distinctm1nd/2025_utahtastic_bsides_badge/hardware/2025_bsides_badge_v2.kicad_sch

## KiCad design hardware/2025_bsides_badge_v2.kicad_sch (2024-11-23)

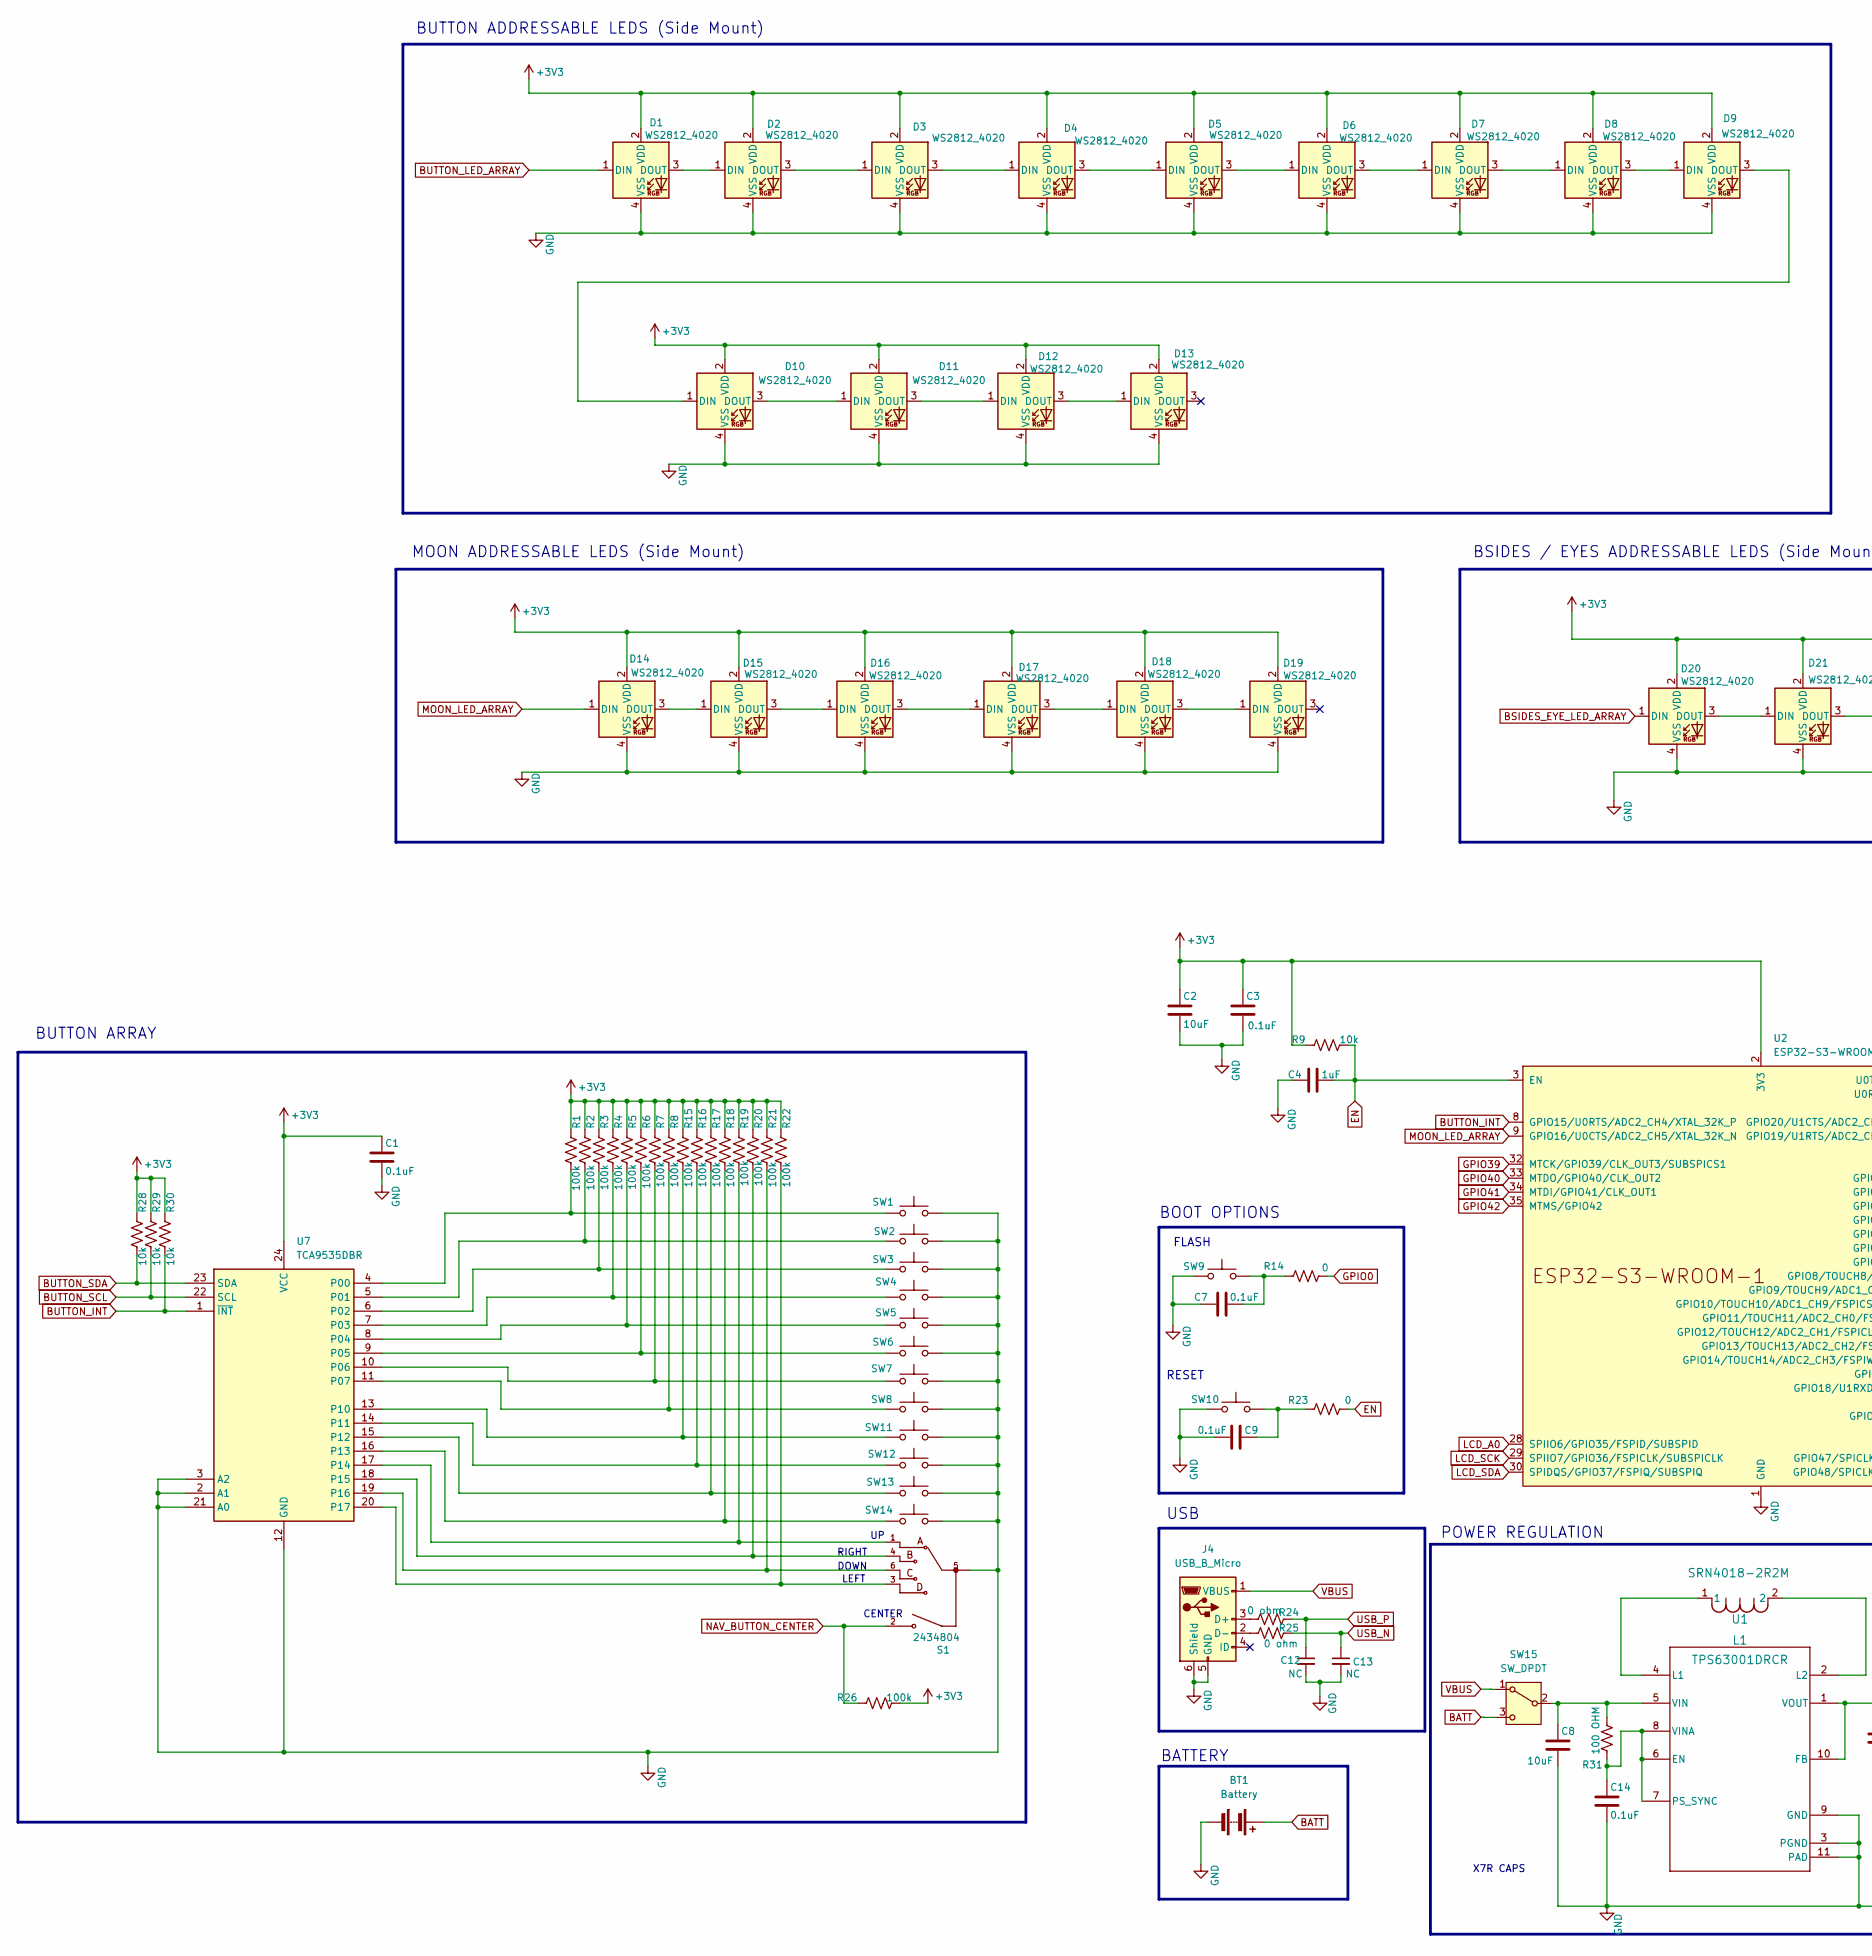
[picture p5: schematic 2025_bsides_badge_v2.kicad_sch, part in row 1, column 1]

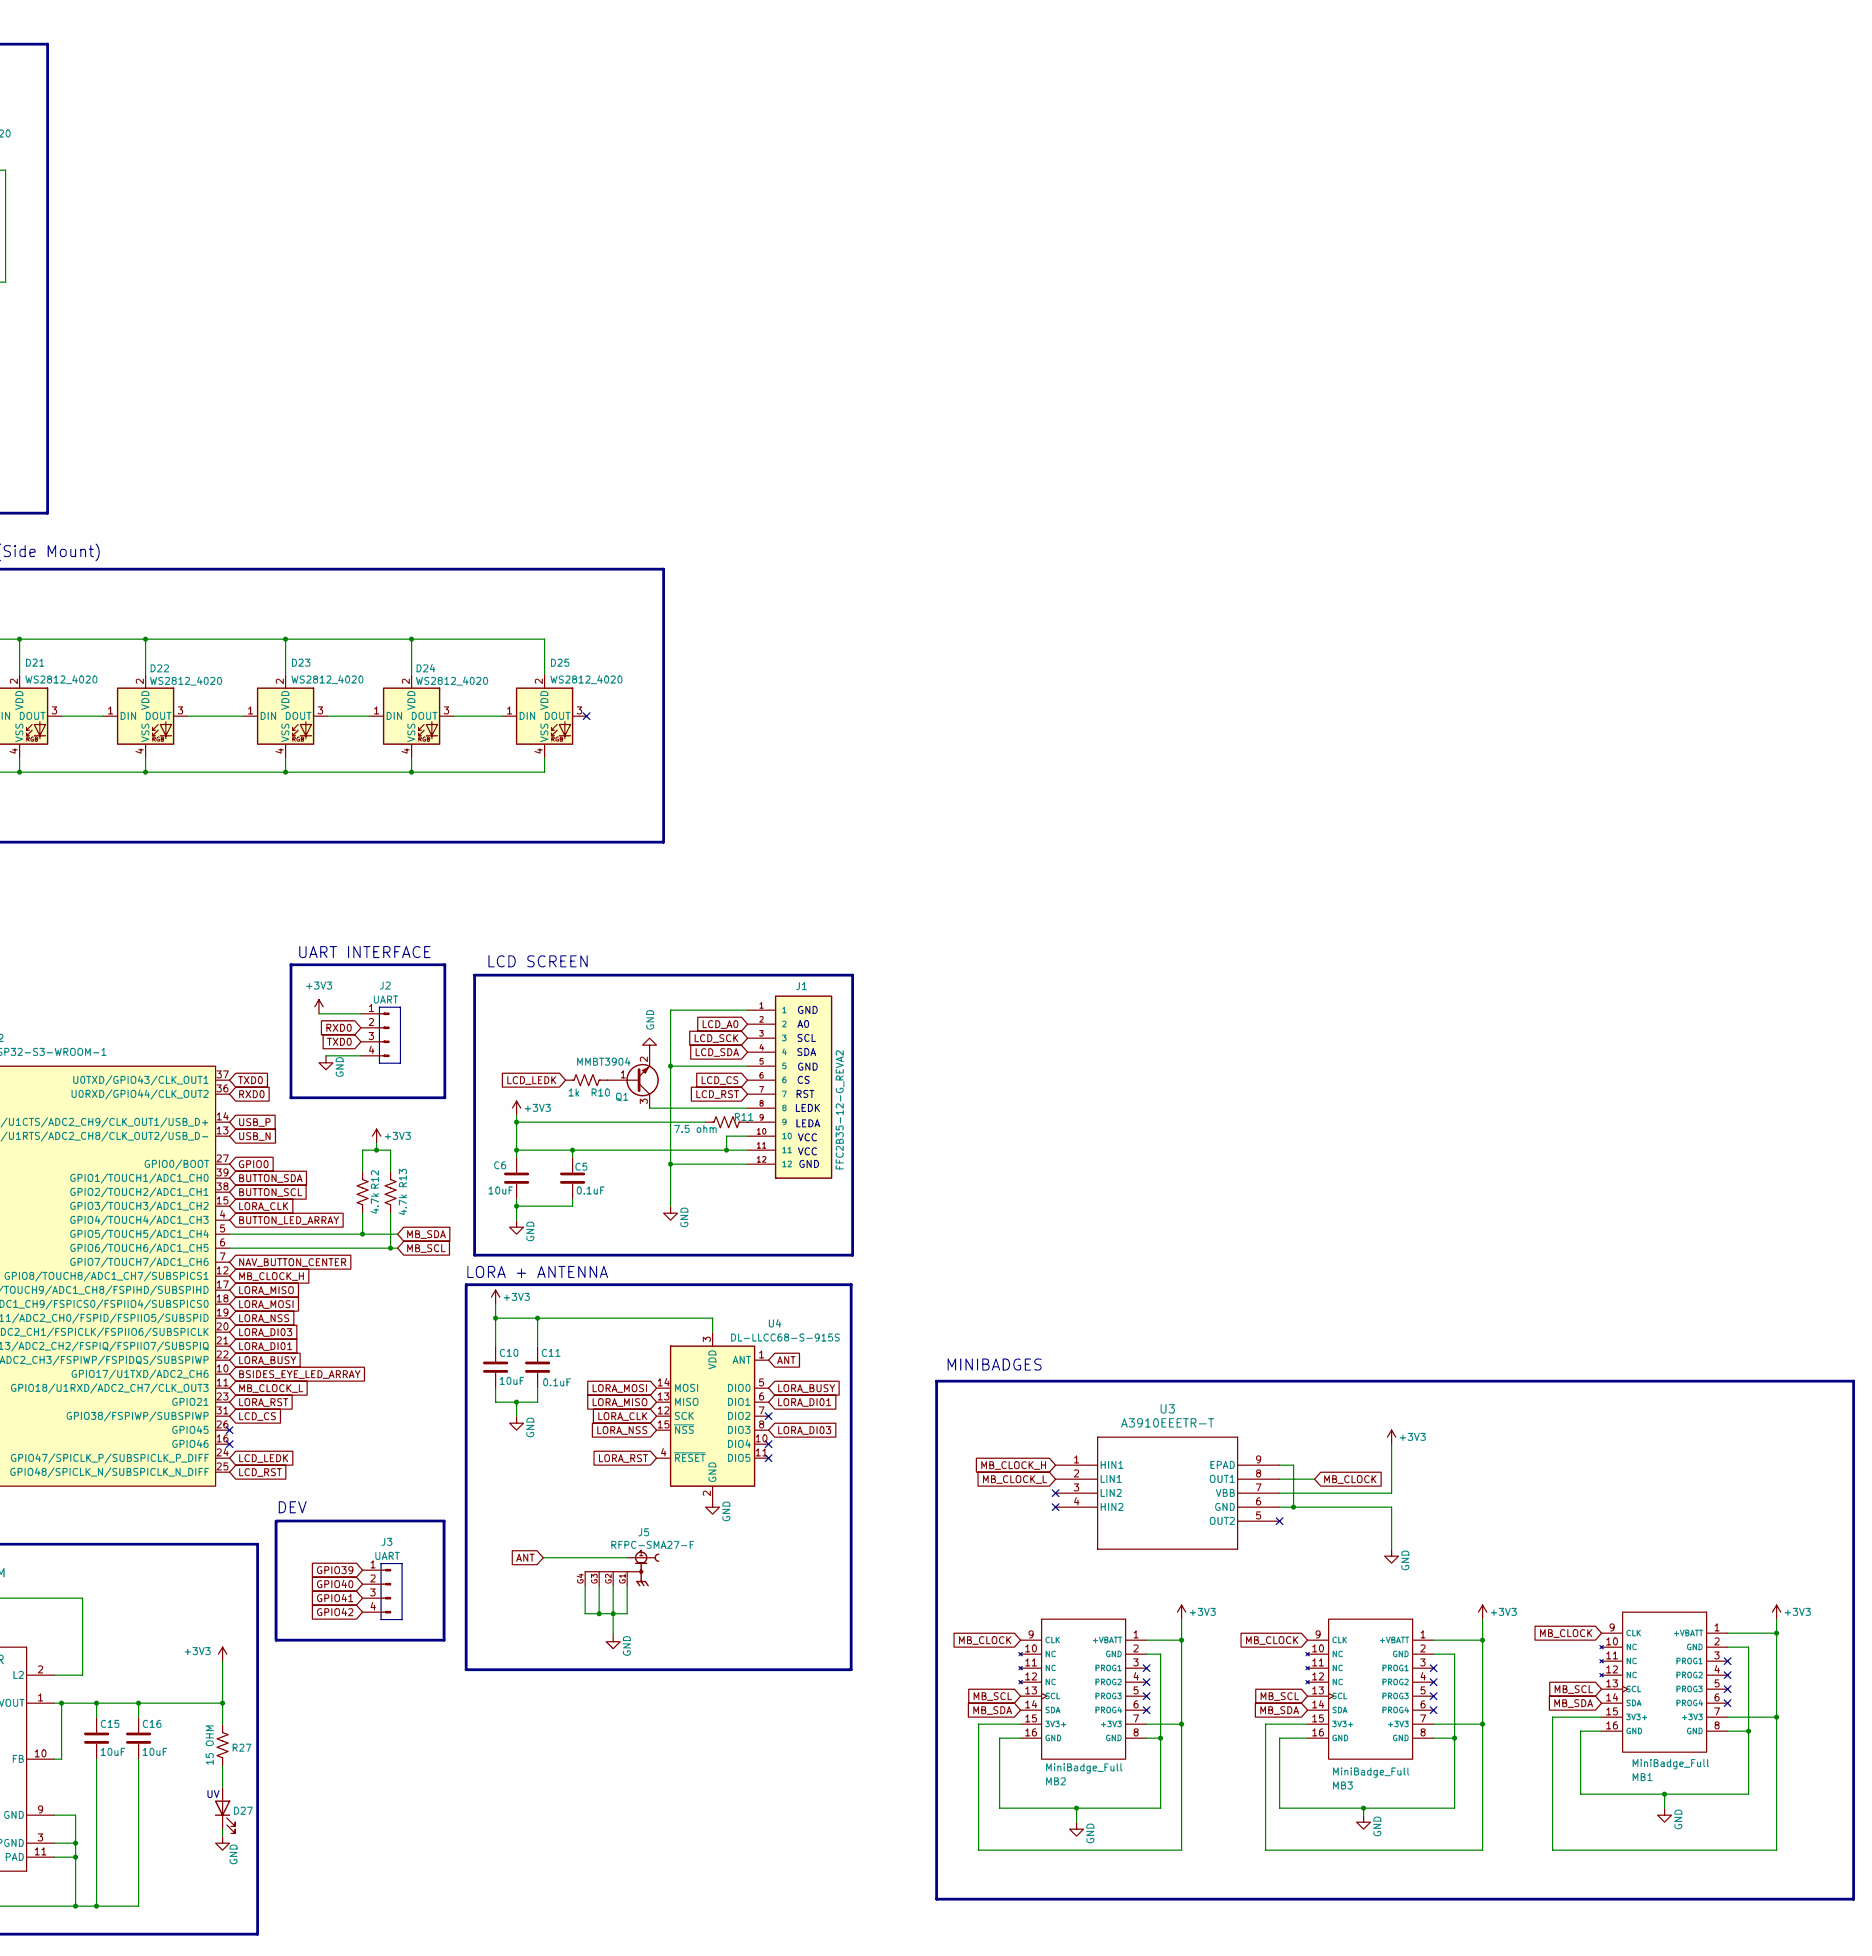
[picture p6: schematic 2025_bsides_badge_v2.kicad_sch, part in row 1, column 2]

Parts:
BT1: Battery; mad_hatter_3_AA_battery
C1, C3, C5, C7, C9, C11, C14: 0.1uF; C_0603_1608Metric_Pad1.08x0.95mm_HandSolder
C2, C6, C8, C10, C15, C16: 10uF; C_0805_2012Metric_Pad1.18x1.45mm_HandSolder
C4: 1uF; C_0603_1608Metric_Pad1.08x0.95mm_HandSolder
C12, C13: NC; C_0603_1608Metric_Pad1.08x0.95mm_HandSolder
D1, D2, D3, D4, D5, D6, D7, D8, D9, D10, D11, D12, D13, D14, D15, D16, D17, D18, D19, D20, D21, D22, D23, D24, D25: WS2812_4020; sk6812-side-a
D27: LED; LED_1206_3216Metric_Pad1.42x1.75mm_HandSolder
J1: FFC2B35-12-G_REVA2; GCT_FFC2B35-12-G_REVA2; PARTREV A2
J2, J3: UART; mad_hatter_sneaky_uart_connector
J4: USB_B_Micro; USB_Micro-B_Amphenol_10118193-0001LF_Horizontal
J5: RFPC-SMA27-F; bsides_RFPC_SMA27_F; PARTREV 1.0
L1: SRN4018-2R2M; L_Bourns-SRN4018
MB1, MB2, MB3: MiniBadge_Full; MiniBadge_Slot_Basic
Q1: MMBT3904; SOT-23
R1, R2, R3, R4, R5, R6, R7, R8, R15, R16, R17, R18, R19, R20, R21, R22, R26: 100k; R_0603_1608Metric_Pad0.98x0.95mm_HandSolder
R9, R28, R29, R30: 10k; R_0603_1608Metric_Pad0.98x0.95mm_HandSolder
R10: 1k; R_0603_1608Metric_Pad0.98x0.95mm_HandSolder
R11: 7.5 ohm; R_0603_1608Metric_Pad0.98x0.95mm_HandSolder
R12, R13: 4.7k; R_0603_1608Metric_Pad0.98x0.95mm_HandSolder
R14, R23: 0; R_0603_1608Metric_Pad0.98x0.95mm_HandSolder
R24, R25: 0 ohm; R_0603_1608Metric_Pad0.98x0.95mm_HandSolder
R27: 15 OHM; R_0603_1608Metric_Pad0.98x0.95mm_HandSolder
R31: 100 OHM; R_0603_1608Metric_Pad0.98x0.95mm_HandSolder
S1: 2434804; nav_switch_2434804_1; PARTREV A
SW1, SW2, SW3, SW4, SW5, SW6, SW7, SW8, SW9, SW10, SW11, SW12, SW13, SW14: SW_Push; button_switch_TL3305A
SW15: SW_DPDT; js202011jaqn
U1: TPS63001DRCR; Texas_DRC0010J
U2: ESP32-S3-WROOM-1
U3: A3910EEETR-T; DFN-8_ALM
U4: DL-LLCC68-S-915S; Ai-Thinker-Ra-01-LoRa
U7: TCA9535DBR; SSOP-24_5.3x8.2mm_P0.65mm

Connections:
+3V3: C1.1, C2.1, C3.1, C5.1, C6.1, C10.1, C11.1, C15.1, C16.1, D1.2 (VDD), D2.2 (VDD), D3.2 (VDD), D4.2 (VDD), D5.2 (VDD), D6.2 (VDD), D7.2 (VDD), D8.2 (VDD), D9.2 (VDD), D10.2 (VDD), D11.2 (VDD), D12.2 (VDD), D13.2 (VDD), D14.2 (VDD), D15.2 (VDD), D16.2 (VDD), D17.2 (VDD), D18.2 (VDD), D19.2 (VDD), D20.2 (VDD), D21.2 (VDD), D22.2 (VDD), D23.2 (VDD), D24.2 (VDD), D25.2 (VDD), J1.10, J1.11, J2.1, MB1.1 (+VBATT), MB1.7 (+3V3), MB1.15 (3V3+), MB2.1 (+VBATT), MB2.7 (+3V3), MB2.15 (3V3+), MB3.1 (+VBATT), MB3.7 (+3V3), MB3.15 (3V3+), R1.1, R2.1, R3.1, R4.1, R5.1, R6.1, R7.1, R8.1, R9.1, R11.1, R12.2, R13.2, R15.1, R16.1, R17.1, R18.1, R19.1, R20.1, R21.1, R22.1, R26.2, R27.1, R28.1, R29.1, R30.1, U1.1 (VOUT), U1.10 (FB), U2.2 (3V3), U3.7 (VBB), U4.3 (VDD), U7.24 (VCC)
ANT: J5.1, U4.1 (ANT)
BATT: BT1.1 (+), SW15.3 (C)
BSIDES_EYE_LED_ARRAY: D20.1 (DIN), U2.10 (GPIO17/U1TXD/ADC2_CH6)
BUTTON_INT: R30.2, U2.8 (GPIO15/U0RTS/ADC2_CH4/XTAL_32K_P), U7.1 (~INT)
BUTTON_LED_ARRAY: D1.1 (DIN), U2.4 (GPIO4/TOUCH4/ADC1_CH3)
BUTTON_SCL: R29.2, U2.38 (GPIO2/TOUCH2/ADC1_CH1), U7.22 (SCL)
BUTTON_SDA: R28.2, U2.39 (GPIO1/TOUCH1/ADC1_CH0), U7.23 (SDA)
EN: C4.1, R9.2, R23.2, U2.3 (EN)
GND: BT1.2 (-), C1.2, C2.2, C3.2, C4.2, C5.2, C6.2, C7.2, C8.2, C9.2, C10.2, C11.2, C12.2, C13.2, C14.2, C15.2, C16.2, D1.4 (VSS), D2.4 (VSS), D3.4 (VSS), D4.4 (VSS), D5.4 (VSS), D6.4 (VSS), D7.4 (VSS), D8.4 (VSS), D9.4 (VSS), D10.4 (VSS), D11.4 (VSS), D12.4 (VSS), D13.4 (VSS), D14.4 (VSS), D15.4 (VSS), D16.4 (VSS), D17.4 (VSS), D18.4 (VSS), D19.4 (VSS), D20.4 (VSS), D21.4 (VSS), D22.4 (VSS), D23.4 (VSS), D24.4 (VSS), D25.4 (VSS), D27.1 (K), J1.1, J1.5, J1.12, J2.4, J4.5 (GND), J4.6 (Shield), J5.G1, J5.G2, J5.G3, J5.G4, MB1.2 (GND), MB1.8 (GND), MB1.16 (GND), MB2.2 (GND), MB2.8 (GND), MB2.16 (GND), MB3.2 (GND), MB3.8 (GND), MB3.16 (GND), Q1.2 (E), S1.5, SW1.2, SW2.2, SW3.2, SW4.2, SW5.2, SW6.2, SW7.2, SW8.2, SW9.1, SW10.1, SW11.2, SW12.2, SW13.2, SW14.2, U1.3 (PGND), U1.9 (GND), U1.11 (PAD), U2.1 (GND), U2.40 (GND), U2.41 (GND), U3.6 (GND), U3.9 (EPAD), U4.2 (GND), U4.9 (GND), U4.16 (GND), U7.2 (A1), U7.3 (A2), U7.12 (GND), U7.21 (A0)
GPIO0: R14.2, U2.27 (GPIO0/BOOT)
GPIO39: J3.1, U2.32 (MTCK/GPIO39/CLK_OUT3/SUBSPICS1)
GPIO40: J3.2, U2.33 (MTDO/GPIO40/CLK_OUT2)
GPIO41: J3.3, U2.34 (MTDI/GPIO41/CLK_OUT1)
GPIO42: J3.4, U2.35 (MTMS/GPIO42)
LCD_A0: J1.2, U2.28 (SPIIO6/GPIO35/FSPID/SUBSPID)
LCD_CS: J1.6, U2.31 (GPIO38/FSPIWP/SUBSPIWP)
LCD_LEDK: R10.1, U2.24 (GPIO47/SPICLK_P/SUBSPICLK_P_DIFF)
LCD_RST: J1.7, U2.25 (GPIO48/SPICLK_N/SUBSPICLK_N_DIFF)
LCD_SCK: J1.3, U2.29 (SPIIO7/GPIO36/FSPICLK/SUBSPICLK)
LCD_SDA: J1.4, U2.30 (SPIDQS/GPIO37/FSPIQ/SUBSPIQ)
LORA_BUSY: U2.22 (GPIO14/TOUCH14/ADC2_CH3/FSPIWP/FSPIDQS/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), U4.5 (DIO0)
LORA_CLK: U2.15 (GPIO3/TOUCH3/ADC1_CH2), U4.12 (SCK)
LORA_DI01: U2.21 (GPIO13/TOUCH13/ADC2_CH2/FSPIQ/FSPIIO7/S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), U4.6 (DIO1)
LORA_DI03: U2.20 (GPIO12/TOUCH12/ADC2_CH1/FSPICLK/FSPIIO6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), U4.8 (DIO3)
LORA_MISO: U2.17 (GPIO9/TOUCH9/ADC1_CH8/FSPIHD/SUBSPIHD), U4.13 (MISO)
LORA_MOSI: U2.18 (GPIO10/TOUCH10/ADC1_CH9/FSPICS0/FSPIIO4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), U4.14 (MOSI)
LORA_NSS: U2.19 (GPIO11/TOUCH11/ADC2_CH0/FSPID/FSPIIO5/S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), U4.15 (~NSS)
LORA_RST: U2.23 (GPIO21), U4.4 (~RESET)
MB_CLOCK: MB1.9 (CLK), MB2.9 (CLK), MB3.9 (CLK), U3.8 (OUT1)
MB_CLOCK_H: U2.12 (GPIO8/TOUCH8/ADC1_CH7/SUBSPICS1), U3.1 (HIN1)
MB_CLOCK_L: U2.11 (GPIO18/U1RXD/ADC2_CH7/CLK_OUT3), U3.2 (LIN1)
MB_SCL: MB1.13 (SCL), MB2.13 (SCL), MB3.13 (SCL), R13.1, U2.6 (GPIO6/TOUCH6/ADC1_CH5)
MB_SDA: MB1.14 (SDA), MB2.14 (SDA), MB3.14 (SDA), R12.1, U2.5 (GPIO5/TOUCH5/ADC1_CH4)
MOON_LED_ARRAY: D14.1 (DIN), U2.9 (GPIO16/U0CTS/ADC2_CH5/XTAL_32K_N)
NAV_BUTTON_CENTER: R26.1, S1.2, U2.7 (GPIO7/TOUCH7/ADC1_CH6)
unnamed: C7.1, R14.1, SW9.2
unnamed: C8.1, R31.1, SW15.2 (B), U1.5 (VIN)
unnamed: C9.1, R23.1, SW10.2
unnamed: C14.1, R31.2, U1.6 (EN), U1.7 (PS_SYNC), U1.8 (VINA)
unnamed: D1.3 (DOUT), D2.1 (DIN)
unnamed: D2.3 (DOUT), D3.1 (DIN)
unnamed: D3.3 (DOUT), D4.1 (DIN)
unnamed: D4.3 (DOUT), D5.1 (DIN)
unnamed: D5.3 (DOUT), D6.1 (DIN)
unnamed: D6.3 (DOUT), D7.1 (DIN)
unnamed: D7.3 (DOUT), D8.1 (DIN)
unnamed: D8.3 (DOUT), D9.1 (DIN)
unnamed: D9.3 (DOUT), D10.1 (DIN)
unnamed: D10.3 (DOUT), D11.1 (DIN)
unnamed: D11.3 (DOUT), D12.1 (DIN)
unnamed: D12.3 (DOUT), D13.1 (DIN)
unnamed: D14.3 (DOUT), D15.1 (DIN)
unnamed: D15.3 (DOUT), D16.1 (DIN)
unnamed: D16.3 (DOUT), D17.1 (DIN)
unnamed: D17.3 (DOUT), D18.1 (DIN)
unnamed: D18.3 (DOUT), D19.1 (DIN)
unnamed: D20.3 (DOUT), D21.1 (DIN)
unnamed: D21.3 (DOUT), D22.1 (DIN)
unnamed: D22.3 (DOUT), D23.1 (DIN)
unnamed: D23.3 (DOUT), D24.1 (DIN)
unnamed: D24.3 (DOUT), D25.1 (DIN)
unnamed: D27.2 (A), R27.2
unnamed: J1.8, Q1.3 (C)
unnamed: J1.9, R11.2
unnamed: J4.2 (D-), R25.2
unnamed: J4.3 (D+), R24.2
unnamed: L1.1, U1.4 (L1)
unnamed: L1.2, U1.2 (L2)
unnamed: Q1.1 (B), R10.2
unnamed: R1.2, SW1.1, U7.4 (P00)
unnamed: R2.2, SW2.1, U7.5 (P01)
unnamed: R3.2, SW3.1, U7.6 (P02)
unnamed: R4.2, SW4.1, U7.7 (P03)
unnamed: R5.2, SW5.1, U7.8 (P04)
unnamed: R6.2, SW6.1, U7.9 (P05)
unnamed: R7.2, SW7.1, U7.10 (P06)
unnamed: R8.2, SW8.1, U7.11 (P07)
unnamed: R15.2, SW11.1, U7.13 (P10)
unnamed: R16.2, SW12.1, U7.14 (P11)
unnamed: R17.2, SW13.1, U7.15 (P12)
unnamed: R18.2, SW14.1, U7.16 (P13)
unnamed: R19.2, S1.1, U7.17 (P14)
unnamed: R20.2, S1.4, U7.18 (P15)
unnamed: R21.2, S1.6, U7.19 (P16)
unnamed: R22.2, S1.3, U7.20 (P17)
RXD0: J2.2, U2.36 (U0RXD/GPIO44/CLK_OUT2)
TXD0: J2.3, U2.37 (U0TXD/GPIO43/CLK_OUT1)
USB_N: C13.1, R25.1, U2.13 (GPIO19/U1RTS/ADC2_CH8/CLK_OUT2/USB_D-)
USB_P: C12.1, R24.1, U2.14 (GPIO20/U1CTS/ADC2_CH9/CLK_OUT1/USB_D+)
VBUS: J4.1 (VBUS), SW15.1 (A)

Notes on the sheet:
UART INTERFACE
LORA + ANTENNA
BATTERY
LEFT
MINIBADGES
GND
DEV
USB
BUTTON ARRAY
VCC
FLASH
LCD SCREEN
MOON ADDRESSABLE LEDS (Side Mount)
POWER REGULATION
BSIDES / EYES ADDRESSABLE LEDS (Side Mount)
RESET
X7R CAPS
CENTER
BUTTON ADDRESSABLE LEDS (Side Mount)
DOWN
SDA
LEDA
BOOT OPTIONS
RIGHT
RST
SCL
LEDK
